igorwolfs/modular-processing-hw/docs/hardware/layout/FMC/rwave_st.png

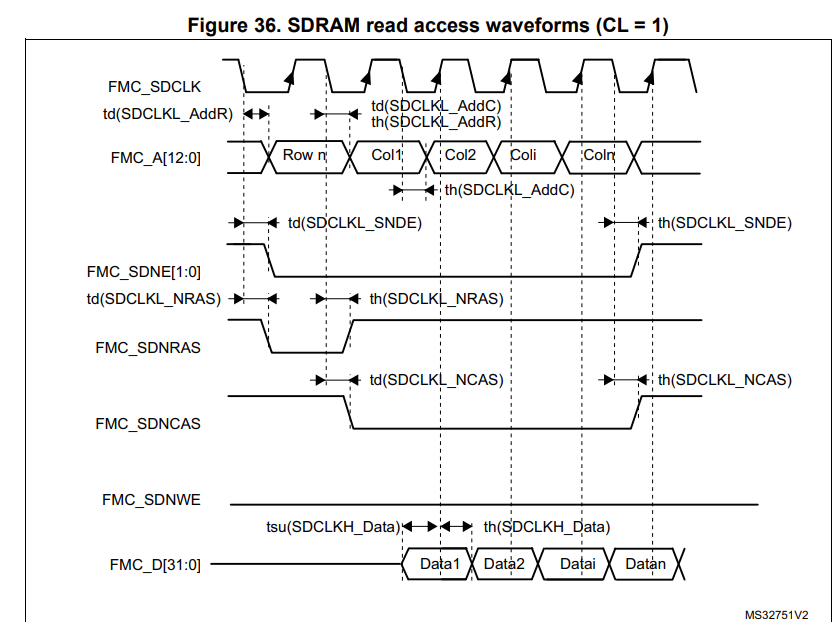
docs/hardware/layout/FMC/rwave_st.png
