igorwolfs/modular-processing-hw/docs/hardware/layout/FMC/wtime_st.png

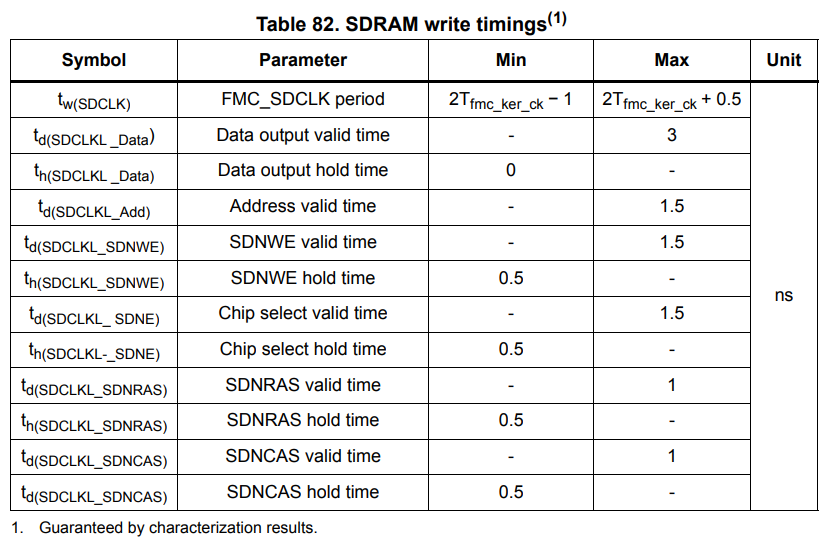
docs/hardware/layout/FMC/wtime_st.png
