igorwolfs/modular-processing-hw/docs/hardware/layout/FMC/wwave_st.png

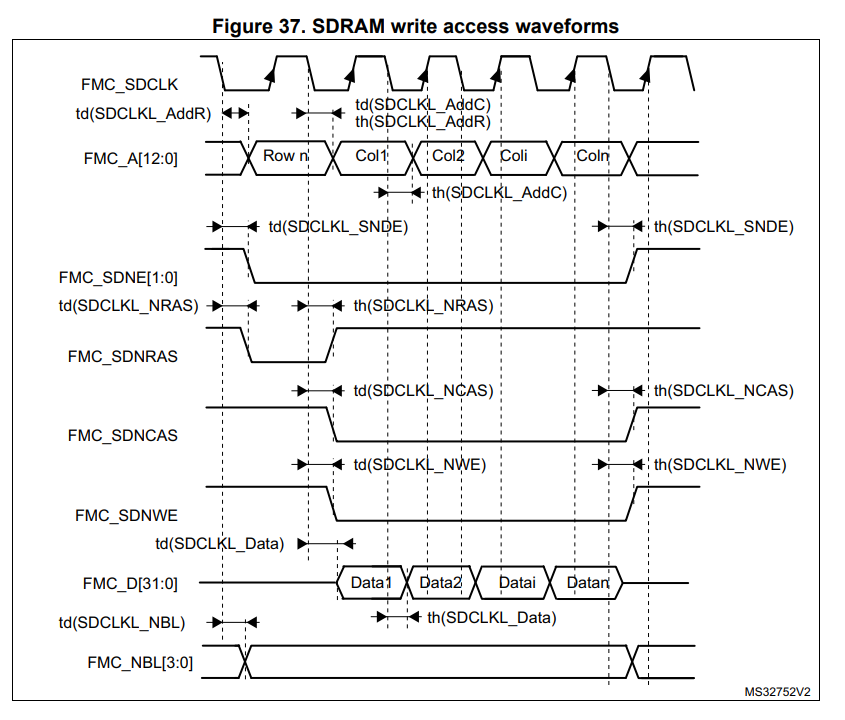
docs/hardware/layout/FMC/wwave_st.png
