igorwolfs/modular-processing-hw/docs/hardware/schematic/mcu/images/adc_resolution.png

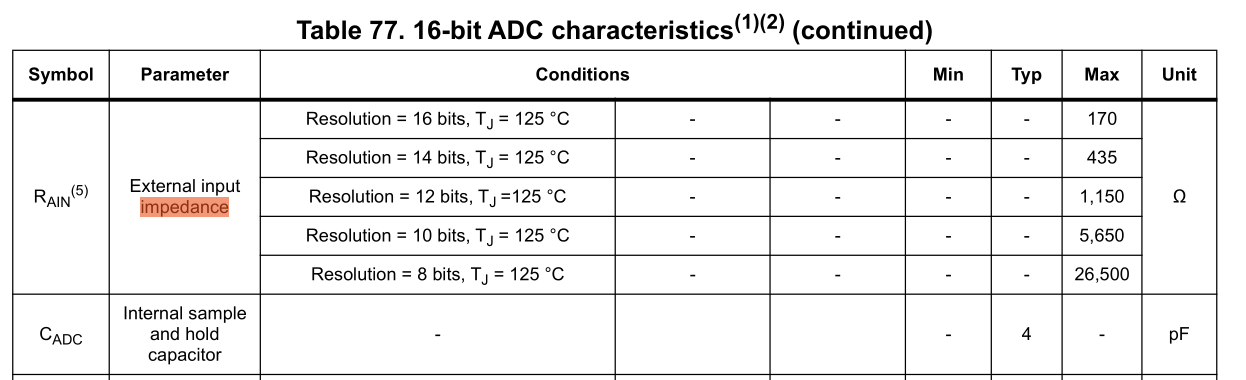
docs/hardware/schematic/mcu/images/adc_resolution.png
