igorwolfs/modular-processing-hw/docs/hardware/schematic/mcu/images/fmc_block_diagram.png

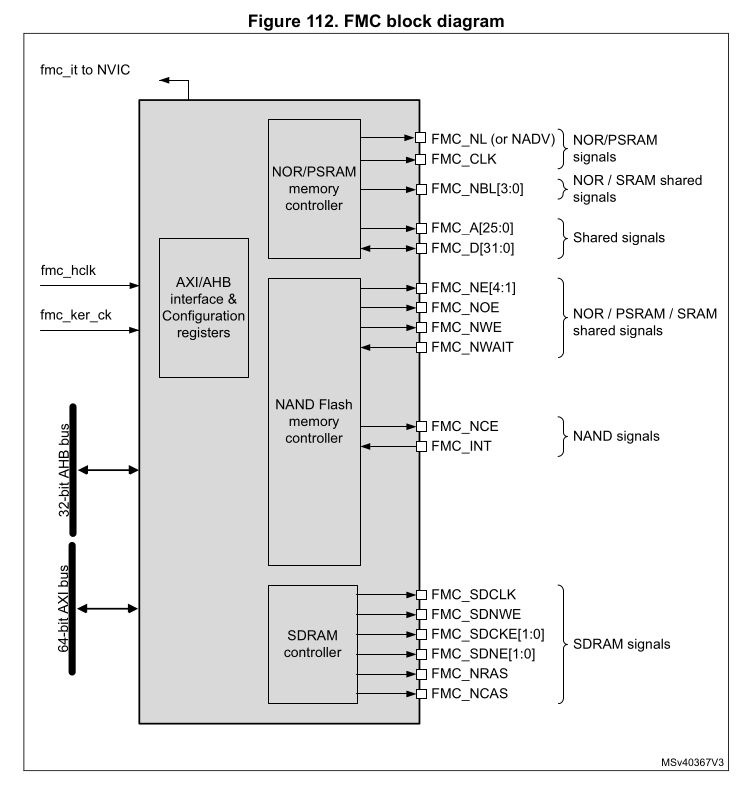
docs/hardware/schematic/mcu/images/fmc_block_diagram.png
