igorwolfs/modular-processing-hw/docs/hardware/schematic/mcu/mcu_protocols/swd_pupd.png

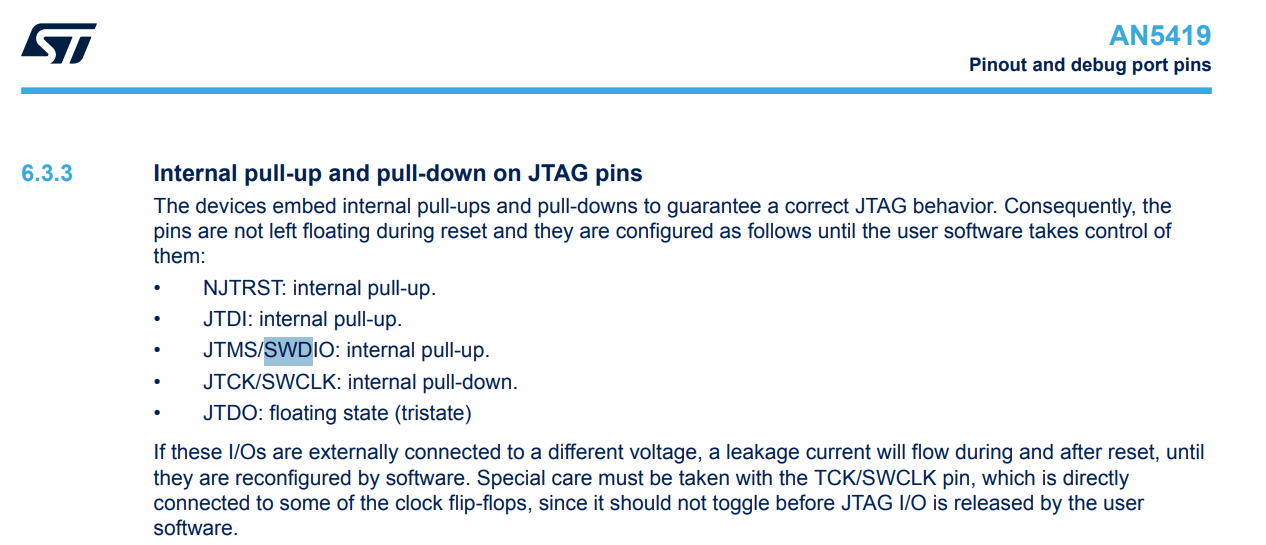
docs/hardware/schematic/mcu/mcu_protocols/swd_pupd.png
