igorwolfs/modular-processing-hw/docs/hardware/schematic/mcu/mcu_protocols/usb_dp_pu.png

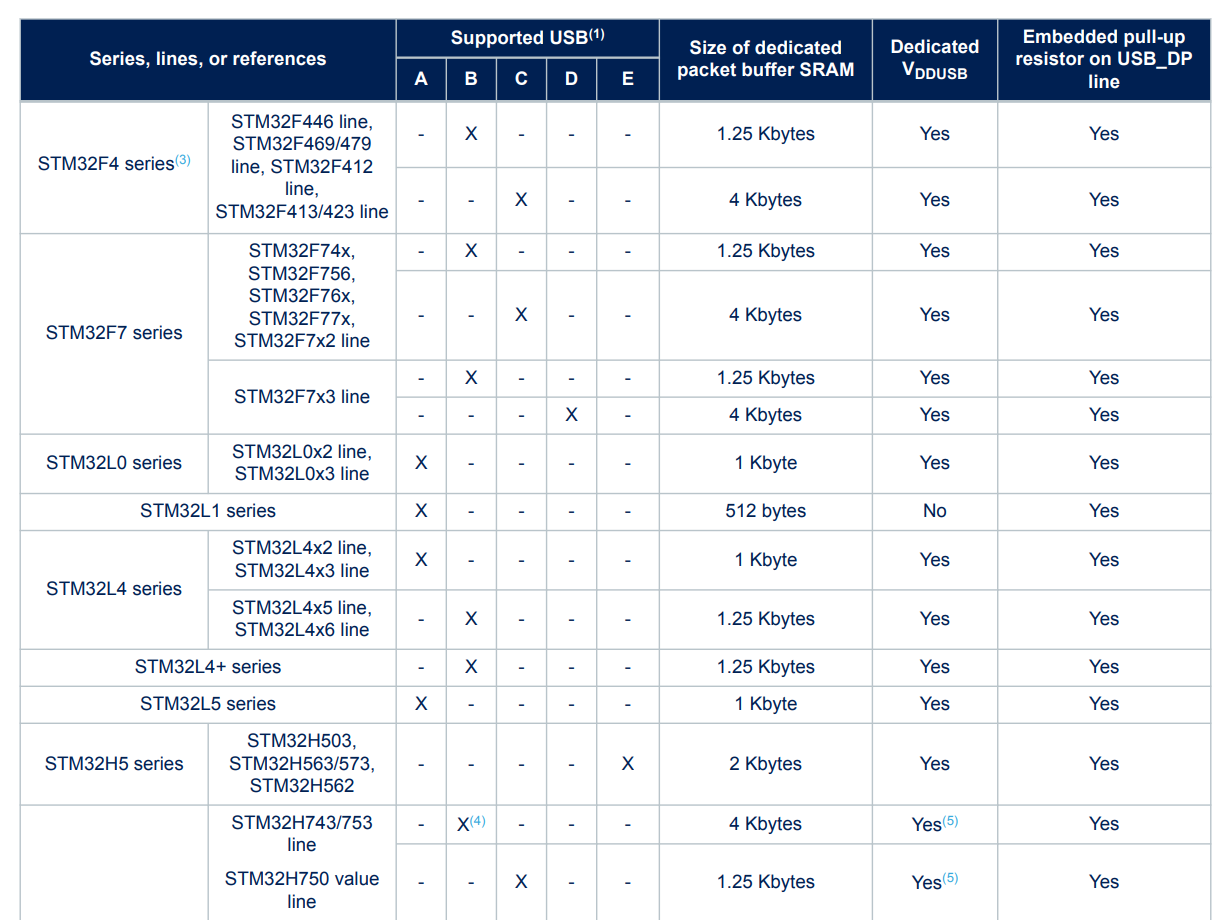
docs/hardware/schematic/mcu/mcu_protocols/usb_dp_pu.png
